DrumPants/DrumPants-Hardware-PCB/Records/Layout2.png

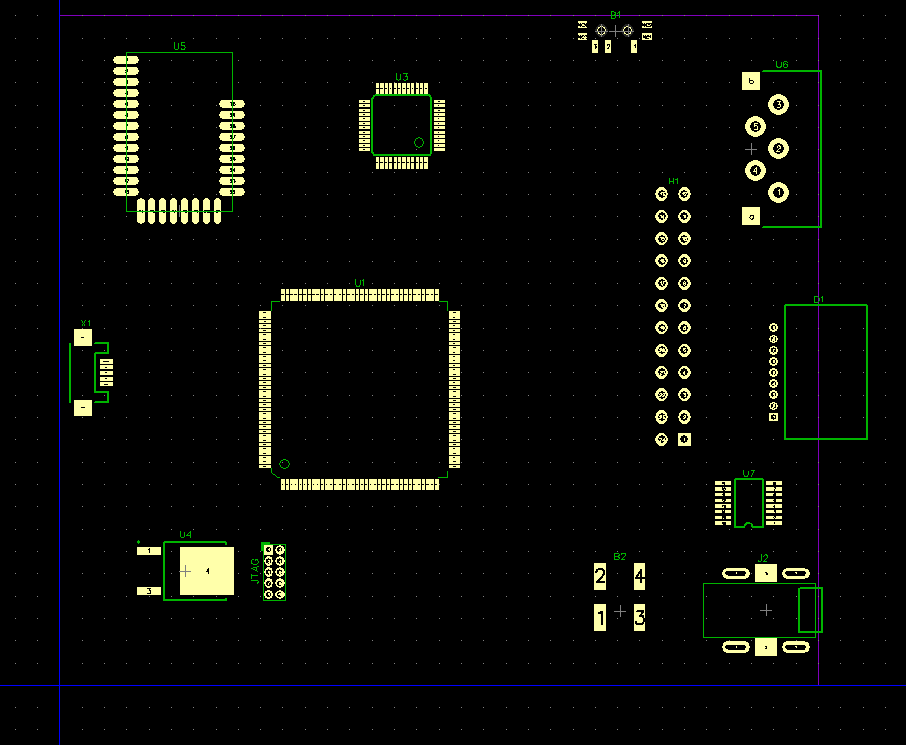
Records/Layout2.png
